J0JIng/GasSentinel/Code/gassentinel-sw/autogen/sl_spidrv_instances.h

#ifndef SL_SPIDRV_INSTANCES_H
#define SL_SPIDRV_INSTANCES_H

#ifdef __cplusplus
extern "C" {
#endif

#include "spidrv.h"
extern SPIDRV_Handle_t sl_spidrv_eusart_mx25_handle;

void sl_spidrv_init_instances(void);

#ifdef __cplusplus
}
#endif

#endif // SL_SPIDRV_INSTANCES_H
