J0JIng/GasSentinel/Code/gassentinel-sw/app_main.h

#ifndef APP_MAIN_H
#define APP_MAIN_H

#ifdef __cplusplus
extern "C" {
#endif

#include "openthread/instance.h"
#include "bsec_datatypes.h"


void app_init(void);

typedef union {
    uint64_t _64b;
    struct {
        uint32_t l;
        uint32_t h;
    } _32b;
} eui_t;

extern eui_t eui;

void app_exit(void);

void app_process_action(void);
void applicationTick(void);

otInstance *otGetInstance(void);
extern struct bme68x_dev bme;
extern uint8_t bsec_state[BSEC_MAX_STATE_BLOB_SIZE];
extern uint8_t work_buffer[BSEC_MAX_WORKBUFFER_SIZE];
void sleepyInit(void);
void setNetworkConfiguration(void);
void initUdp(void);

void sl_ot_create_instance(void);
void sl_ot_cli_init(void);


#define IP_LED_PORT      gpioPortC
#define IP_LED_PIN       7
#define ACT_LED_PORT     gpioPortC
#define ACT_LED_PIN      6
#define ERR_LED_PORT     gpioPortC
#define ERR_LED_PIN      5

#define I2C_SCL_PORT     gpioPortB
#define I2C_SCL_PIN      1
#define I2C_SDA_PORT     gpioPortB
#define I2C_SDA_PIN      0
#define TS_INT_PORT      gpioPortC
#define TS_INT_PIN       0
#define VBAT_SENSE_PORT  gpioPortC
#define VBAT_SENSE_PIN   1
#define SW_PWR_SRC_PORT  gpioPortB
#define SW_PWR_SRC_PIN   3



#ifdef __cplusplus
}
#endif /* __cplusplus */


#endif // APP_MAIN_H
