J0JIng/GasSentinel/Code/gassentinel-sw/app_coap.cpp

#include "app_coap.h"
#include <app_main.h>
#include <assert.h>
#include <openthread-core-config.h>
#include <openthread/config.h>

#include <openthread/cli.h>
#include <openthread/diag.h>
#include <openthread/tasklet.h>
#include <openthread/thread.h>

#include "openthread-system.h"
#include "sl_component_catalog.h"

#include <openthread/coap.h>
#include "utils/code_utils.h"

#include "em_gpio.h"
#include "stdio.h"
#include "string.h"

namespace coap {

static otIp6Address selfAddr;

/*** srp registration related params ***/
#define PERMISSIONS_URI "permissions"
static otCoapResource mResource_PERMISSIONS;
static otIp6Address brAddr;
static const char mPERMISSIONSUriPath[] = PERMISSIONS_URI;
static char resource[16];
bool appCoapConnectionEstablished = false;
static char resource_name[32];

/*** unused dns discovery ***/
static bool discovered = false;
static bool registered = false;


static uint32_t txFailCtr = 0;
const uint8_t device_type = 254U;

// fwd declarations
static bool parseIntoBuffer(const sensor::sig_if_t *in);
static void coapTxMsg(void);

static char buffer[255];

constexpr static char *payload_fmt = "%d,%.8lx%.8lx,%lu,%ld,%lu,%lu,%lu,%lu,%d,%lu";
constexpr static char *common_resource = "common";
const char *ack = "ack";
const char *nack = "nack";


MailboxQueue<sensor::sig_if_t, COAP_MAILBOX_QUEUE_DEPTH> ux_queue;


volatile uint32_t vsense_batt;

void permissionsHandler(void *aContext, otMessage *aMessage, const otMessageInfo *aMessageInfo)
{
    // GPIO_PinOutSet(IP_LED_PORT, IP_LED_PIN);
    // printIPv6Addr(&aMessageInfo->mPeerAddr);
    brAddr = aMessageInfo->mPeerAddr;
    selfAddr = aMessageInfo->mSockAddr;
    otError error = OT_ERROR_NONE;
    otMessage *responseMessage;
    uint16_t offset;
    otCoapCode responseCode = OT_COAP_CODE_CHANGED;
    otCoapCode messageCode = otCoapMessageGetCode(aMessage);

    responseMessage = otCoapNewMessage((otInstance *)aContext, NULL);
    otEXPECT_ACTION(responseMessage != NULL, error = OT_ERROR_NO_BUFS);
    otCoapMessageInitResponse(responseMessage, aMessage,
                              OT_COAP_TYPE_ACKNOWLEDGMENT, responseCode);
    otCoapMessageSetToken(responseMessage, otCoapMessageGetToken(aMessage),
                          otCoapMessageGetTokenLength(aMessage));
    otCoapMessageSetPayloadMarker(responseMessage);

    offset = otMessageGetOffset(aMessage);
    otMessageRead(aMessage, offset, resource_name, sizeof(resource_name) - 1);
    // otCliOutputFormat("Unique resource ID: %s\n", resource_name);

    if (OT_COAP_CODE_GET == messageCode)
    {

        error = otMessageAppend(responseMessage, ack, strlen((const char *)ack));
        otEXPECT(OT_ERROR_NONE == error);
        error = otCoapSendResponse((otInstance *)aContext, responseMessage,
                                   aMessageInfo);
        otEXPECT(OT_ERROR_NONE == error);
    }
    else
    {
        error = otMessageAppend(responseMessage, nack, strlen((const char *)nack));
        otCoapMessageSetCode(responseMessage, OT_COAP_CODE_METHOD_NOT_ALLOWED);
        otEXPECT(OT_ERROR_NONE == error);
        error = otCoapSendResponse((otInstance *)aContext, responseMessage,
                                   aMessageInfo);
        otEXPECT(OT_ERROR_NONE == error);
    }

exit:
    if (error != OT_ERROR_NONE && responseMessage != NULL)
    {
        otMessageFree(responseMessage);
    }
    appCoapConnectionEstablished = true;
    GPIO_PinOutClear(IP_LED_PORT, IP_LED_PIN);
}

void init(void) {
	discovered = true;
	otCoapStart(otGetInstance(), OT_DEFAULT_COAP_PORT);

    mResource_PERMISSIONS.mUriPath = mPERMISSIONSUriPath;
    mResource_PERMISSIONS.mContext = otGetInstance();
    mResource_PERMISSIONS.mHandler = &permissionsHandler;

    strncpy((char *)mPERMISSIONSUriPath, PERMISSIONS_URI, sizeof(PERMISSIONS_URI));
    otCoapAddResource(otGetInstance(), &mResource_PERMISSIONS);


	snprintf(resource, 16, "%.8lx%.8lx", eui._32b.h, eui._32b.l);
	//otCliOutputFormat("[APP COAP][I] resource name: %s\n", resource);
}

/*
void updateAddr(otIp6Address server_ip)
{
	destAddr = server_ip;
}
*/

bool service(void)
{
	if(!appCoapConnectionEstablished) return false;
	if(ux_queue.empty()) {
		//otCliOutputFormat("empty queue\n");
		return false;
	}
	sensor::sig_if_t data = ux_queue.front();
	//otCliOutputFormat("[APP COAP][I] this <---ux_queue--- sensor  pop\n");
	if(parseIntoBuffer(&data)) {
		ux_queue.pop();
		GPIO_PinOutSet(IP_LED_PORT, IP_LED_PIN);
		coapTxMsg();
		GPIO_PinOutClear(IP_LED_PORT, IP_LED_PIN);
		//otCliOutputFormat("[APP COAP][I] CoAP message sent\n");
		return true;
	}
	return false;
}


static bool parseIntoBuffer(const sensor::sig_if_t *in)
{
	uint32_t iaq = static_cast<uint32_t>(in->iaq.first);
	int32_t temp = static_cast<int32_t>(in->comp_temp.first*COAP_LFACTOR_DECIMAL_COUNT);
	uint32_t hum = static_cast<uint32_t>(in->comp_hum.first*COAP_LFACTOR_DECIMAL_COUNT);
	uint32_t pres = static_cast<uint32_t>(in->pres.first);

	uint32_t cl1 = static_cast<uint32_t>(in->class1.first*COAP_LFACTOR_DECIMAL_COUNT);
	uint32_t cl2 = static_cast<uint32_t>(in->class2.first*COAP_LFACTOR_DECIMAL_COUNT);
	int8_t rssi;

	otThreadGetParentLastRssi(otGetInstance(), &rssi);

	uint32_t ret = snprintf(buffer, 254, payload_fmt, device_type, eui._32b.h,
			 eui._32b.l ,iaq, temp, hum, pres, cl1, cl2, rssi, vsense_batt);
	if(ret >= 254) return false;

	return true;
}

static void coapTxMsg(void) {

	otError error = OT_ERROR_NONE;
	otMessage *message = NULL;
	otMessageInfo messageInfo;
	uint16_t payloadLength = 0;

	// Default parameters
	otCoapType coapType = OT_COAP_TYPE_CONFIRMABLE;
	message = otCoapNewMessage(otGetInstance(), NULL);

	otCoapMessageInit(message, coapType, OT_COAP_CODE_PUT);
	otCoapMessageGenerateToken(message, OT_COAP_DEFAULT_TOKEN_LENGTH);
	error = otCoapMessageAppendUriPathOptions(message,/* registered ? resource :*/ resource_name);
	registered = true;
	otEXPECT(OT_ERROR_NONE == error);

	payloadLength = strlen(buffer);

	if (payloadLength > 0) {
		error = otCoapMessageSetPayloadMarker(message);
		otEXPECT(OT_ERROR_NONE == error);
	}

	// Embed content into message if given
	if (payloadLength > 0) {
		error = otMessageAppend(message, buffer, payloadLength);
		otEXPECT(OT_ERROR_NONE == error);
	}

	memset(&messageInfo, 0, sizeof(messageInfo));
	messageInfo.mPeerAddr = brAddr;
	messageInfo.mPeerPort = OT_DEFAULT_COAP_PORT; //TODO revert
	error = otCoapSendRequestWithParameters(otGetInstance(), message,
			&messageInfo, NULL, NULL,
			NULL);
	otEXPECT(OT_ERROR_NONE == error);

	exit: if ((error != OT_ERROR_NONE) && (message != NULL)) {
		txFailCtr = 0;
		otMessageFree(message);
	}

	if (error != OT_ERROR_NONE) {
		txFailCtr++;
	}

}

}
